dragutin-oreski/pokedex/res/classified/dex_entries/images/airplane.jpg

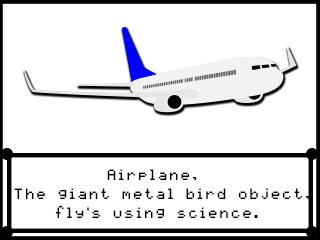
res/classified/dex_entries/images/airplane.jpg
