dragutin-oreski/pokedex/res/classified/dex_entries/images/apple.jpg

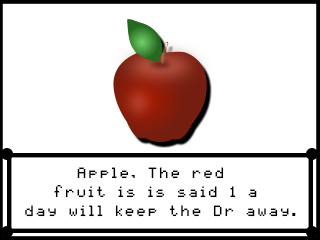
res/classified/dex_entries/images/apple.jpg
