dragutin-oreski/pokedex/res/classified/dex_entries/images/backpack.jpg

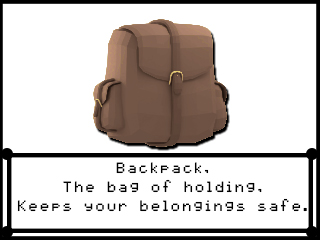
res/classified/dex_entries/images/backpack.jpg
