dragutin-oreski/pokedex/res/classified/dex_entries/images/banana.jpg

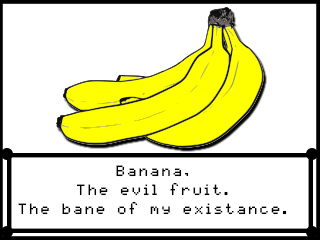
res/classified/dex_entries/images/banana.jpg
