dragutin-oreski/pokedex/res/classified/dex_entries/images/baseball bat.jpg

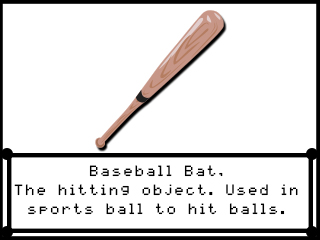
res/classified/dex_entries/images/baseball bat.jpg
