dragutin-oreski/pokedex/res/classified/dex_entries/images/baseball glove.jpg

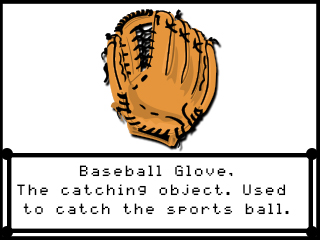
res/classified/dex_entries/images/baseball glove.jpg
