dragutin-oreski/pokedex/res/classified/dex_entries/images/bear.jpg

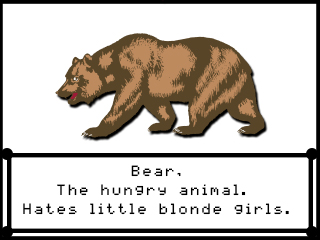
res/classified/dex_entries/images/bear.jpg
