dragutin-oreski/pokedex/res/classified/dex_entries/images/bed.jpg

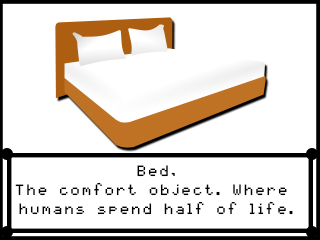
res/classified/dex_entries/images/bed.jpg
