dragutin-oreski/pokedex/res/classified/dex_entries/images/bench.jpg

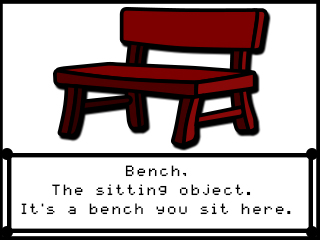
res/classified/dex_entries/images/bench.jpg
