dragutin-oreski/pokedex/res/classified/dex_entries/images/bike.jpg

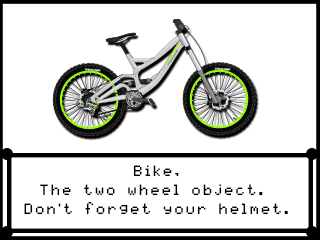
res/classified/dex_entries/images/bike.jpg
