dragutin-oreski/pokedex/res/classified/dex_entries/images/bird.jpg

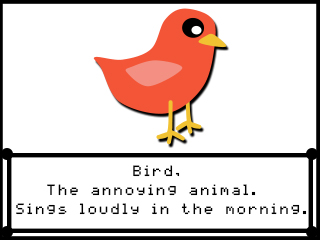
res/classified/dex_entries/images/bird.jpg
