dragutin-oreski/pokedex/res/classified/dex_entries/images/blender.jpg

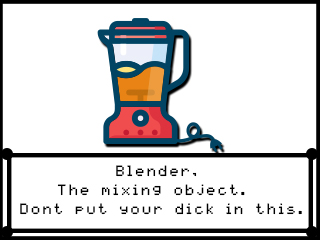
res/classified/dex_entries/images/blender.jpg
