dragutin-oreski/pokedex/res/classified/dex_entries/images/boat.jpg

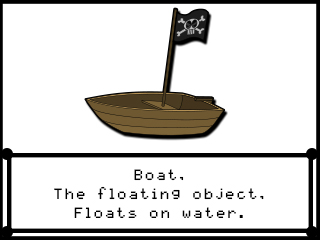
res/classified/dex_entries/images/boat.jpg
