dragutin-oreski/pokedex/res/classified/dex_entries/images/bobi.jpg

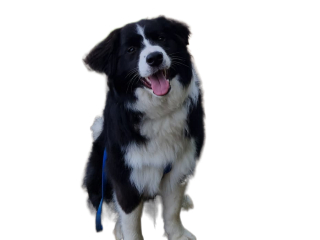
res/classified/dex_entries/images/bobi.jpg
