dragutin-oreski/pokedex/res/classified/dex_entries/images/book.jpg

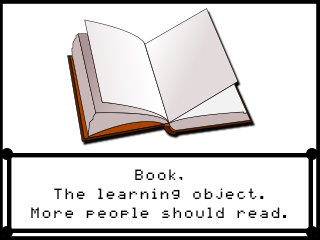
res/classified/dex_entries/images/book.jpg
