dragutin-oreski/pokedex/res/classified/dex_entries/images/bottle.jpg

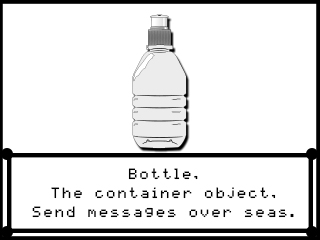
res/classified/dex_entries/images/bottle.jpg
