dragutin-oreski/pokedex/res/classified/dex_entries/images/bowl.jpg

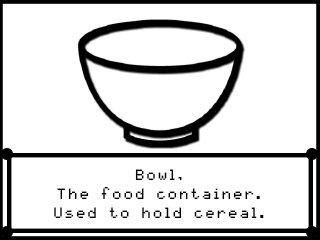
res/classified/dex_entries/images/bowl.jpg
