dragutin-oreski/pokedex/res/classified/dex_entries/images/broccoli.jpg

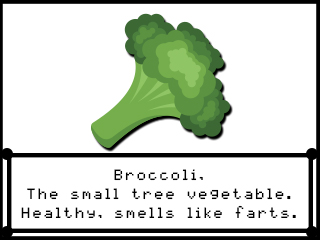
res/classified/dex_entries/images/broccoli.jpg
