dragutin-oreski/pokedex/res/classified/dex_entries/images/bus.jpg

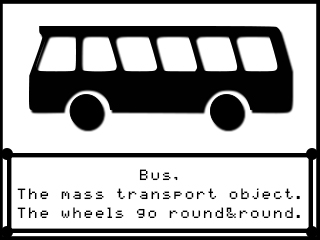
res/classified/dex_entries/images/bus.jpg
