dragutin-oreski/pokedex/res/classified/dex_entries/images/cake.jpg

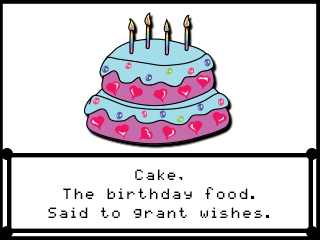
res/classified/dex_entries/images/cake.jpg
