dragutin-oreski/pokedex/res/classified/dex_entries/images/car.jpg

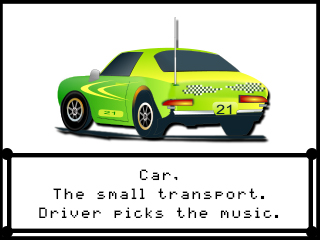
res/classified/dex_entries/images/car.jpg
