dragutin-oreski/pokedex/res/classified/dex_entries/images/carrot.jpg

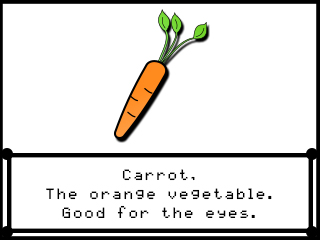
res/classified/dex_entries/images/carrot.jpg
