dragutin-oreski/pokedex/res/classified/dex_entries/images/cat.jpg

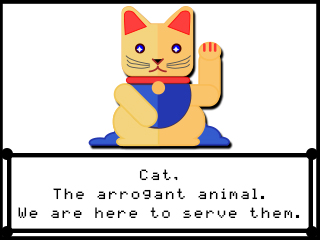
res/classified/dex_entries/images/cat.jpg
