dragutin-oreski/pokedex/res/classified/dex_entries/images/cell phone.jpg

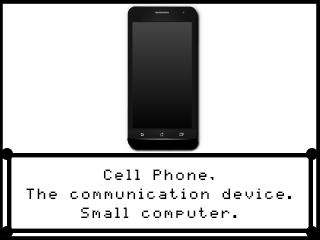
res/classified/dex_entries/images/cell phone.jpg
