dragutin-oreski/pokedex/res/classified/dex_entries/images/chair.jpg

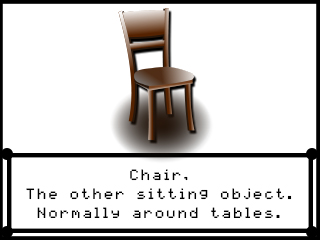
res/classified/dex_entries/images/chair.jpg
