dragutin-oreski/pokedex/res/classified/dex_entries/images/clock.jpg

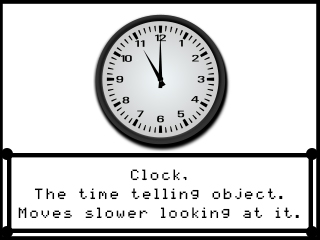
res/classified/dex_entries/images/clock.jpg
