dragutin-oreski/pokedex/res/classified/dex_entries/images/couch.jpg

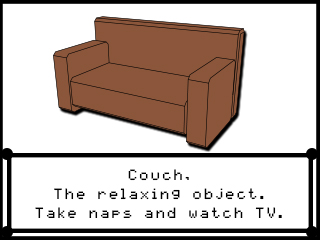
res/classified/dex_entries/images/couch.jpg
