dragutin-oreski/pokedex/res/classified/dex_entries/images/cow.jpg

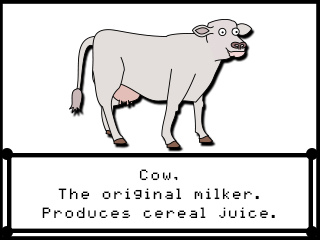
res/classified/dex_entries/images/cow.jpg
