dragutin-oreski/pokedex/res/classified/dex_entries/images/cup.jpg

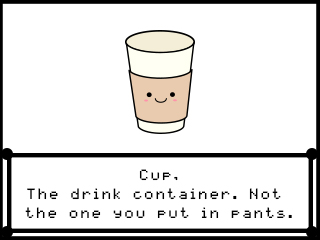
res/classified/dex_entries/images/cup.jpg
