dragutin-oreski/pokedex/res/classified/dex_entries/images/desk.jpg

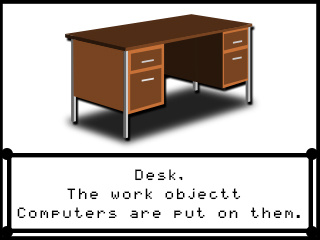
res/classified/dex_entries/images/desk.jpg
