dragutin-oreski/pokedex/res/classified/dex_entries/images/dining table.jpg

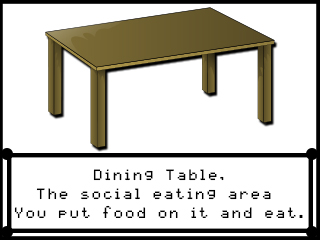
res/classified/dex_entries/images/dining table.jpg
