dragutin-oreski/pokedex/res/classified/dex_entries/images/donut.jpg

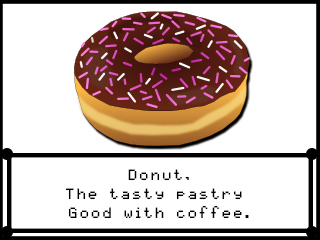
res/classified/dex_entries/images/donut.jpg
