dragutin-oreski/pokedex/res/classified/dex_entries/images/door.jpg

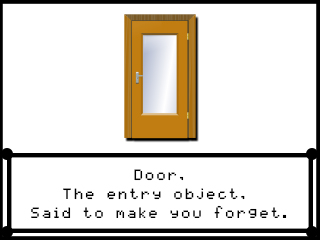
res/classified/dex_entries/images/door.jpg
