dragutin-oreski/pokedex/res/classified/dex_entries/images/elephant.jpg

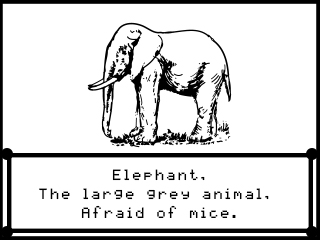
res/classified/dex_entries/images/elephant.jpg
