dragutin-oreski/pokedex/res/classified/dex_entries/images/eye glasses.jpg

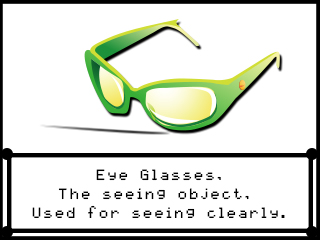
res/classified/dex_entries/images/eye glasses.jpg
