dragutin-oreski/pokedex/res/classified/dex_entries/images/fire hydrant.jpg

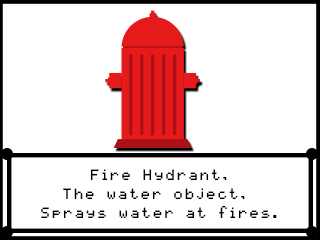
res/classified/dex_entries/images/fire hydrant.jpg
