dragutin-oreski/pokedex/res/classified/dex_entries/images/fork.jpg

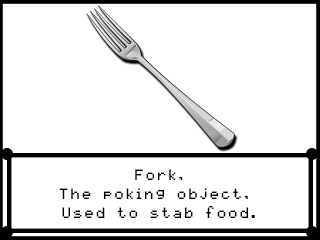
res/classified/dex_entries/images/fork.jpg
