dragutin-oreski/pokedex/res/classified/dex_entries/images/frisbee.jpg

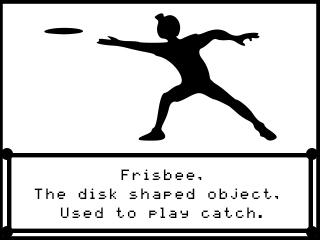
res/classified/dex_entries/images/frisbee.jpg
