dragutin-oreski/pokedex/res/classified/dex_entries/images/giraffe.jpg

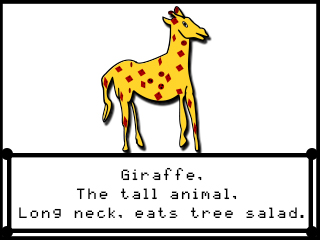
res/classified/dex_entries/images/giraffe.jpg
