dragutin-oreski/pokedex/res/classified/dex_entries/images/hair brush.jpg

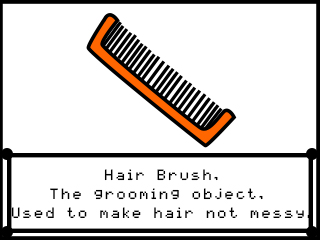
res/classified/dex_entries/images/hair brush.jpg
