dragutin-oreski/pokedex/res/classified/dex_entries/images/hair drier.jpg

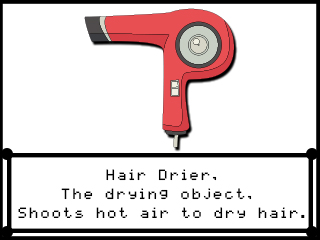
res/classified/dex_entries/images/hair drier.jpg
