dragutin-oreski/pokedex/res/classified/dex_entries/images/handbag.jpg

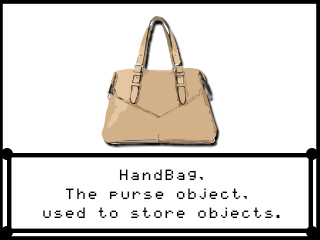
res/classified/dex_entries/images/handbag.jpg
