dragutin-oreski/pokedex/res/classified/dex_entries/images/hat.jpg

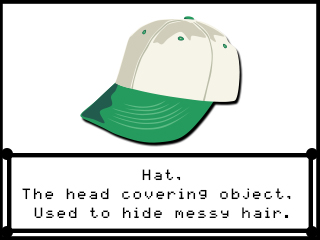
res/classified/dex_entries/images/hat.jpg
