dragutin-oreski/pokedex/res/classified/dex_entries/images/horse.jpg

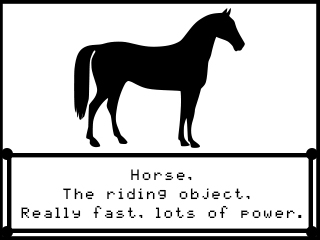
res/classified/dex_entries/images/horse.jpg
