dragutin-oreski/pokedex/res/classified/dex_entries/images/hot dog.jpg

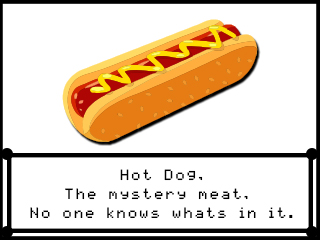
res/classified/dex_entries/images/hot dog.jpg
