dragutin-oreski/pokedex/res/classified/dex_entries/images/keyboard.jpg

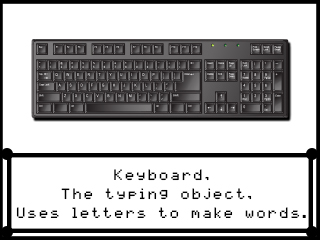
res/classified/dex_entries/images/keyboard.jpg
