dragutin-oreski/pokedex/res/classified/dex_entries/images/kite.jpg

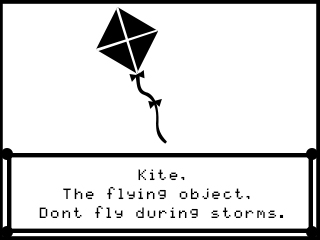
res/classified/dex_entries/images/kite.jpg
