dragutin-oreski/pokedex/res/classified/dex_entries/images/knife.jpg

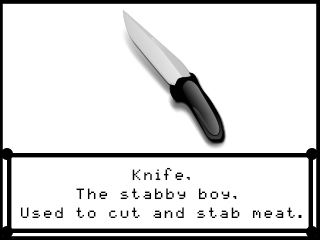
res/classified/dex_entries/images/knife.jpg
