dragutin-oreski/pokedex/res/classified/dex_entries/images/laptop.jpg

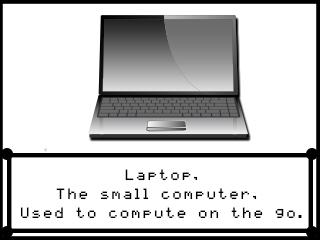
res/classified/dex_entries/images/laptop.jpg
