dragutin-oreski/pokedex/res/classified/dex_entries/images/microwave.jpg

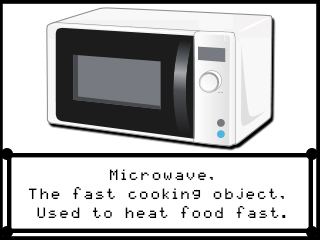
res/classified/dex_entries/images/microwave.jpg
