dragutin-oreski/pokedex/res/classified/dex_entries/images/mirror.jpg

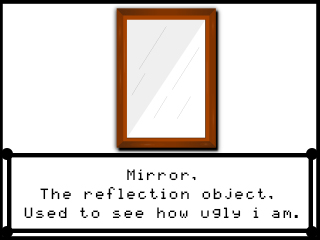
res/classified/dex_entries/images/mirror.jpg
