dragutin-oreski/pokedex/res/classified/dex_entries/images/motorcycle.jpg

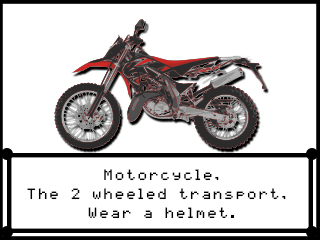
res/classified/dex_entries/images/motorcycle.jpg
