dragutin-oreski/pokedex/res/classified/dex_entries/images/mouse.jpg

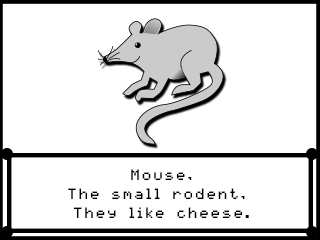
res/classified/dex_entries/images/mouse.jpg
