dragutin-oreski/pokedex/res/classified/dex_entries/images/orange.jpg

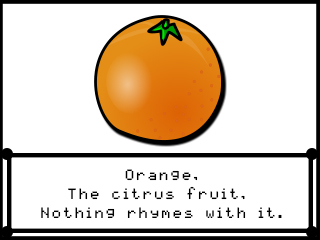
res/classified/dex_entries/images/orange.jpg
