dragutin-oreski/pokedex/res/classified/dex_entries/images/oven.jpg

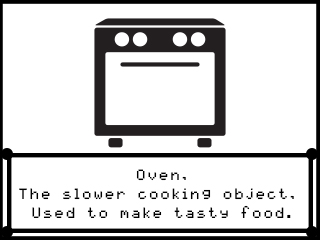
res/classified/dex_entries/images/oven.jpg
