dragutin-oreski/pokedex/res/classified/dex_entries/images/parking meter.jpg

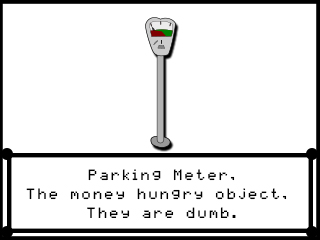
res/classified/dex_entries/images/parking meter.jpg
