dragutin-oreski/pokedex/res/classified/dex_entries/images/person.jpg

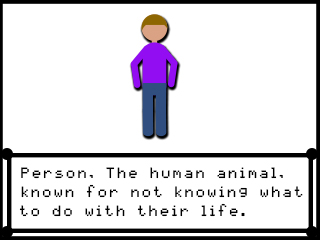
res/classified/dex_entries/images/person.jpg
