dragutin-oreski/pokedex/res/classified/dex_entries/images/pizza.jpg

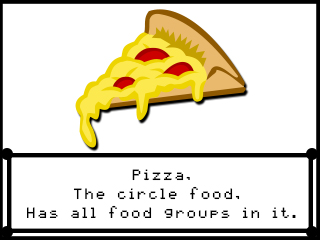
res/classified/dex_entries/images/pizza.jpg
