dragutin-oreski/pokedex/res/classified/dex_entries/images/plate.jpg

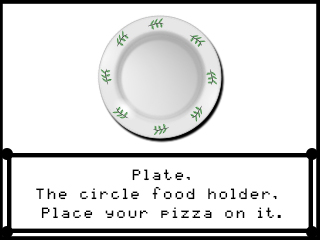
res/classified/dex_entries/images/plate.jpg
