dragutin-oreski/pokedex/res/classified/dex_entries/images/pokeball.jpg

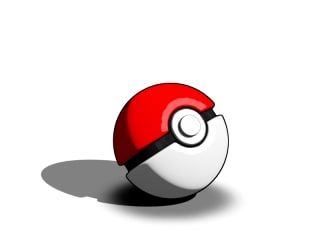
res/classified/dex_entries/images/pokeball.jpg
