dragutin-oreski/pokedex/res/classified/dex_entries/images/potted plant.jpg

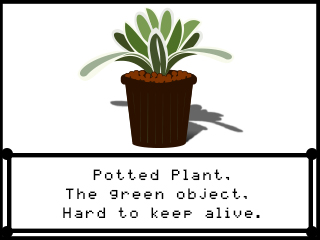
res/classified/dex_entries/images/potted plant.jpg
