dragutin-oreski/pokedex/res/classified/dex_entries/images/refrigerator.jpg

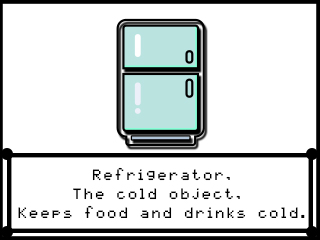
res/classified/dex_entries/images/refrigerator.jpg
