dragutin-oreski/pokedex/res/classified/dex_entries/images/remote.jpg

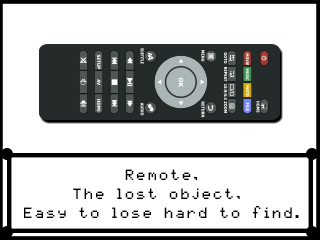
res/classified/dex_entries/images/remote.jpg
