dragutin-oreski/pokedex/res/classified/dex_entries/images/sandwich.jpg

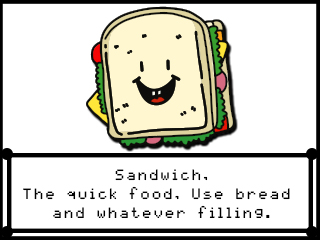
res/classified/dex_entries/images/sandwich.jpg
