dragutin-oreski/pokedex/res/classified/dex_entries/images/scissors.jpg

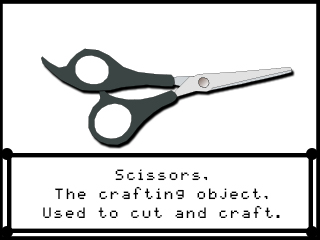
res/classified/dex_entries/images/scissors.jpg
