dragutin-oreski/pokedex/res/classified/dex_entries/images/sheep.jpg

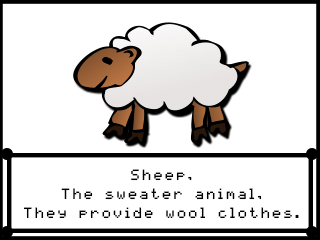
res/classified/dex_entries/images/sheep.jpg
