dragutin-oreski/pokedex/res/classified/dex_entries/images/shoe.jpg

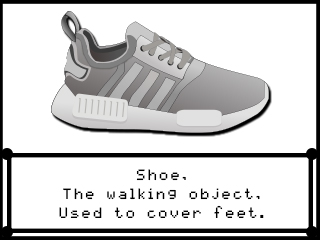
res/classified/dex_entries/images/shoe.jpg
