dragutin-oreski/pokedex/res/classified/dex_entries/images/sink.jpg

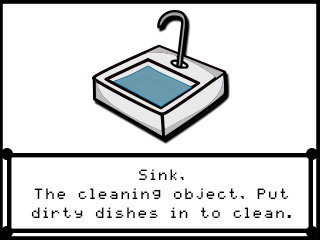
res/classified/dex_entries/images/sink.jpg
