dragutin-oreski/pokedex/res/classified/dex_entries/images/skateboard.jpg

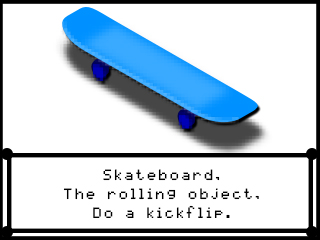
res/classified/dex_entries/images/skateboard.jpg
