dragutin-oreski/pokedex/res/classified/dex_entries/images/skis.jpg

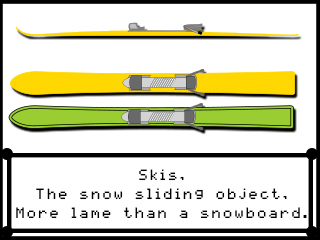
res/classified/dex_entries/images/skis.jpg
