dragutin-oreski/pokedex/res/classified/dex_entries/images/snowboard.jpg

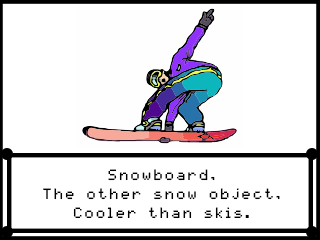
res/classified/dex_entries/images/snowboard.jpg
