dragutin-oreski/pokedex/res/classified/dex_entries/images/spoon.jpg

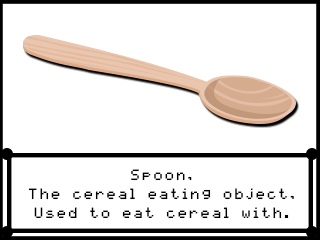
res/classified/dex_entries/images/spoon.jpg
