dragutin-oreski/pokedex/res/classified/dex_entries/images/sports ball.jpg

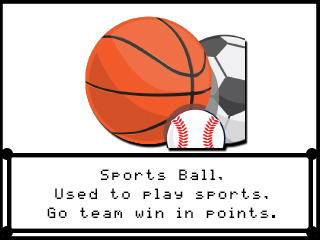
res/classified/dex_entries/images/sports ball.jpg
