dragutin-oreski/pokedex/res/classified/dex_entries/images/stop sign.jpg

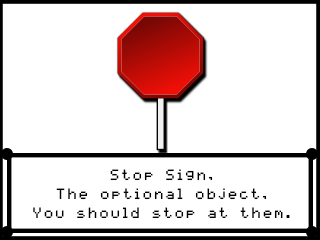
res/classified/dex_entries/images/stop sign.jpg
