dragutin-oreski/pokedex/res/classified/dex_entries/images/street sign.jpg

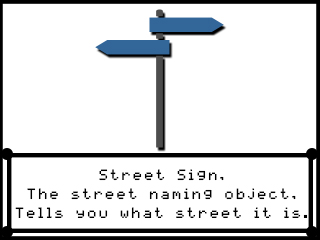
res/classified/dex_entries/images/street sign.jpg
