dragutin-oreski/pokedex/res/classified/dex_entries/images/suitcase.jpg

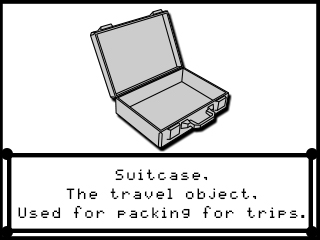
res/classified/dex_entries/images/suitcase.jpg
