dragutin-oreski/pokedex/res/classified/dex_entries/images/surfboard.jpg

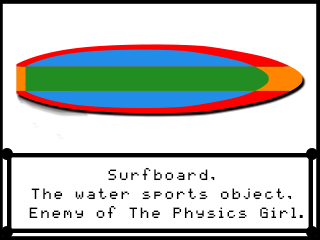
res/classified/dex_entries/images/surfboard.jpg
