dragutin-oreski/pokedex/res/classified/dex_entries/images/teddy bear.jpg

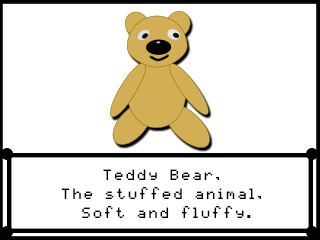
res/classified/dex_entries/images/teddy bear.jpg
