dragutin-oreski/pokedex/res/classified/dex_entries/images/tennis racket.jpg

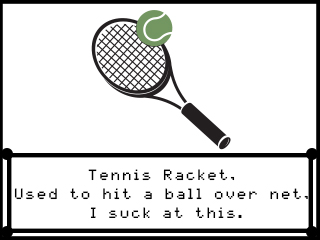
res/classified/dex_entries/images/tennis racket.jpg
