dragutin-oreski/pokedex/res/classified/dex_entries/images/tie.jpg

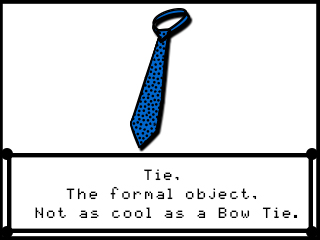
res/classified/dex_entries/images/tie.jpg
