dragutin-oreski/pokedex/res/classified/dex_entries/images/toaster.jpg

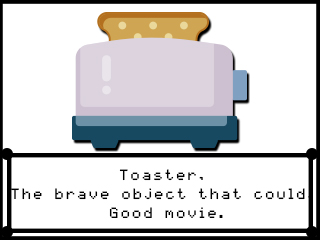
res/classified/dex_entries/images/toaster.jpg
