dragutin-oreski/pokedex/res/classified/dex_entries/images/toilet.jpg

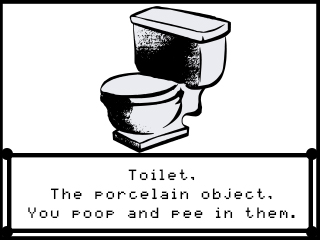
res/classified/dex_entries/images/toilet.jpg
