dragutin-oreski/pokedex/res/classified/dex_entries/images/toothbrush.jpg

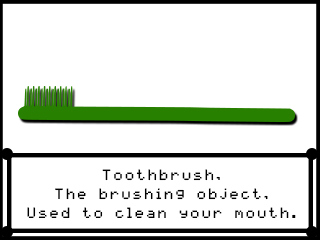
res/classified/dex_entries/images/toothbrush.jpg
