dragutin-oreski/pokedex/res/classified/dex_entries/images/traffic light.jpg

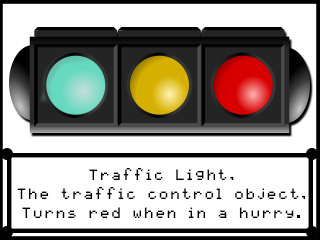
res/classified/dex_entries/images/traffic light.jpg
