dragutin-oreski/pokedex/res/classified/dex_entries/images/train.jpg

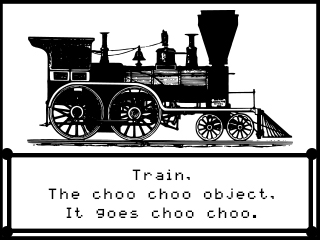
res/classified/dex_entries/images/train.jpg
