dragutin-oreski/pokedex/res/classified/dex_entries/images/truck.jpg

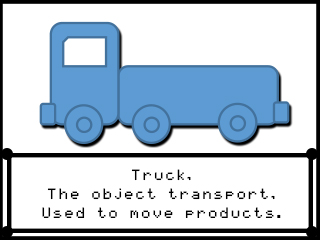
res/classified/dex_entries/images/truck.jpg
