dragutin-oreski/pokedex/res/classified/dex_entries/images/tv.jpg

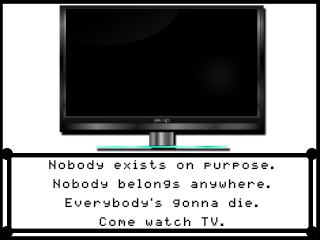
res/classified/dex_entries/images/tv.jpg
