dragutin-oreski/pokedex/res/classified/dex_entries/images/umbrella.jpg

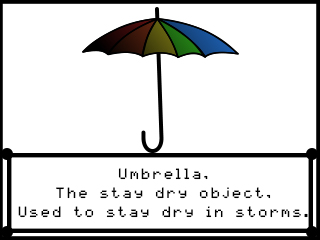
res/classified/dex_entries/images/umbrella.jpg
