dragutin-oreski/pokedex/res/classified/dex_entries/images/vase.jpg

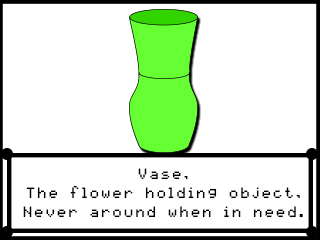
res/classified/dex_entries/images/vase.jpg
