dragutin-oreski/pokedex/res/classified/dex_entries/images/window.jpg

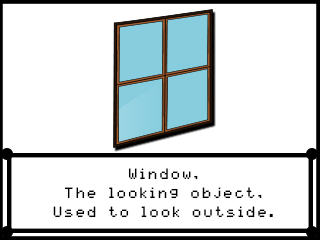
res/classified/dex_entries/images/window.jpg
