dragutin-oreski/pokedex/res/classified/dex_entries/images/wine glass.jpg

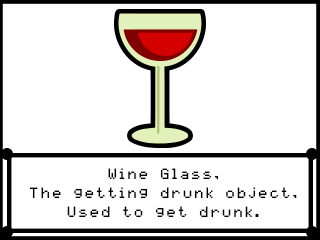
res/classified/dex_entries/images/wine glass.jpg
