dragutin-oreski/pokedex/res/classified/dex_entries/images/zebra.jpg

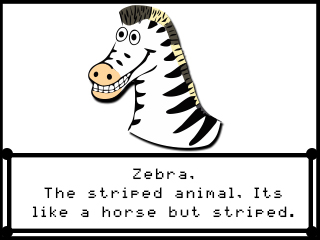
res/classified/dex_entries/images/zebra.jpg
